azasypkin/kroneum/hw/pcb/Rev_0.6/demo/kroneum-pcb.png

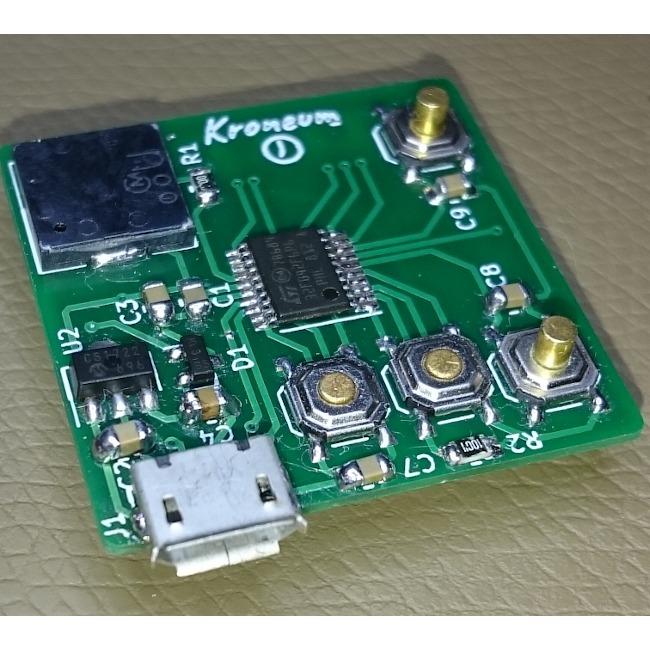
hw/pcb/Rev_0.6/demo/kroneum-pcb.png
