azasypkin/kroneum/sw/firmware/api/src/usb/commands.rs

mod adc;
mod alarm;
mod beeper;
mod flash;
mod keyboard;
mod radio;
mod system;

pub use self::adc::ADCCommand;
pub use self::alarm::AlarmCommand;
pub use self::beeper::BeeperCommand;
pub use self::flash::FlashCommand;
pub use self::keyboard::{KeyModifiers, KeyboardCommand, MediaKey};
pub use self::radio::RadioCommand;
pub use self::system::SystemCommand;
