azasypkin/kroneum/sw/cli/src/ui.rs

use crate::device::{Device, DeviceInfo};
use actix_files as fs;
use actix_web::{web, App, HttpResponse, HttpServer, Responder};
use core::convert::TryFrom;
use kroneum_api::{
    adc::ADCChannel,
    beeper::tone::Tone,
    flash::storage_slot::StorageSlot,
    time::Time,
    usb::commands::{KeyModifiers, MediaKey},
};
use serde_derive::{Deserialize, Serialize};

#[derive(Deserialize)]
struct ADCParams {
    channel: u8,
}

#[derive(Deserialize)]
#[serde(remote = "KeyModifiers")]
struct KeyModifiersDef {
    #[serde(rename(deserialize = "leftCtrl"))]
    left_ctrl: bool,
    #[serde(rename(deserialize = "leftShift"))]
    left_shift: bool,
    #[serde(rename(deserialize = "leftAlt"))]
    left_alt: bool,
    #[serde(rename(deserialize = "leftGUI"))]
    left_gui: bool,
    #[serde(rename(deserialize = "rightCtrl"))]
    right_ctrl: bool,
    #[serde(rename(deserialize = "rightShift"))]
    right_shift: bool,
    #[serde(rename(deserialize = "rightAlt"))]
    right_alt: bool,
    #[serde(rename(deserialize = "rightGUI"))]
    right_gui: bool,
}

#[derive(Deserialize)]
struct KeyParams {
    #[serde(rename(deserialize = "keyCode"))]
    key_code: u8,
    delay: u8,
    #[serde(with = "KeyModifiersDef")]
    modifiers: KeyModifiers,
}

#[derive(Deserialize)]
struct MediaKeyParams {
    #[serde(rename(deserialize = "keyCode"))]
    key_code: u8,
    delay: u8,
}

#[derive(Serialize)]
struct SystemInfoResponse {
    id: String,
    #[serde(rename(serialize = "flashSizeKb"))]
    flash_size_kb: u16,
}

#[derive(Serialize)]
struct InfoResponse {
    device: DeviceInfo,
    system: SystemInfoResponse,
}

#[derive(Deserialize)]
struct SetAlarmParams {
    alarm: String,
}

#[derive(Deserialize)]
struct WriteFlashParams {
    slot: u8,
    value: u8,
}

async fn adc(params: web::Path<ADCParams>) -> impl Responder {
    match ADCChannel::try_from(params.channel) {
        Ok(channel) => {
            HttpResponse::Ok().json(Device::create().unwrap().adc_read(channel).unwrap())
        }
        Err(message) => HttpResponse::BadRequest().body(message),
    }
}

async fn alarm_get() -> impl Responder {
    let device = Device::create().unwrap();
    let alarm = Time::from_seconds(device.get_alarm().unwrap().as_secs() as u32);
    HttpResponse::Ok().json(format!(
        "{:02}h {:02}m {:02}s",
        alarm.hours, alarm.minutes, alarm.seconds
    ))
}

async fn alarm_set(alarm: web::Json<SetAlarmParams>) -> impl Responder {
    match alarm
        .0
        .alarm
        .parse::<humantime::Duration>()
        .or_else(|err| Err(format!("Failed to parse alarm: {:?}", err)))
    {
        Ok(duration) => match Device::create().unwrap().set_alarm(duration.into()) {
            Ok(_) => HttpResponse::NoContent().finish(),
            Err(message) => HttpResponse::InternalServerError().body(message),
        },
        Err(message) => HttpResponse::BadRequest().body(message),
    }
}

async fn beep() -> impl Responder {
    let device = Device::create().unwrap();
    device.beeper_beep(1).unwrap();
    HttpResponse::NoContent()
}

async fn echo(info: web::Json<Vec<u8>>) -> impl Responder {
    HttpResponse::Ok().json(
        Device::create()
            .unwrap()
            .system_echo(info.as_ref())
            .unwrap(),
    )
}

async fn radio_transmit(info: web::Json<Vec<u8>>) -> impl Responder {
    match Device::create().unwrap().radio_transmit(info.as_ref()) {
        Ok(_) => HttpResponse::NoContent().finish(),
        Err(message) => HttpResponse::InternalServerError().body(message),
    }
}

async fn radio_receive() -> impl Responder {
    HttpResponse::Ok().json(Device::create().unwrap().radio_receive().unwrap())
}

async fn radio_status() -> impl Responder {
    HttpResponse::Ok().json(Device::create().unwrap().radio_status().unwrap())
}

async fn play(tones: web::Json<Vec<(u8, u8)>>) -> impl Responder {
    let device = Device::create().unwrap();
    device
        .beeper_melody(
            tones
                .iter()
                .map(|(note, duration)| Tone::new(*note, *duration))
                .collect::<Vec<Tone>>()
                .as_ref(),
        )
        .unwrap();
    HttpResponse::NoContent()
}

async fn flash_read() -> impl Responder {
    let device = Device::create().unwrap();
    HttpResponse::Ok().json(vec![
        device.read_flash(StorageSlot::Configuration).unwrap(),
        device.read_flash(StorageSlot::Custom(1)).unwrap(),
        device.read_flash(StorageSlot::Custom(2)).unwrap(),
        device.read_flash(StorageSlot::Custom(3)).unwrap(),
        device.read_flash(StorageSlot::Custom(4)).unwrap(),
    ])
}

async fn flash_write(flash: web::Json<WriteFlashParams>) -> impl Responder {
    match StorageSlot::try_from(flash.slot) {
        Ok(slot) => match Device::create().unwrap().write_flash(slot, flash.value) {
            Ok(_) => HttpResponse::NoContent().finish(),
            Err(message) => HttpResponse::InternalServerError().body(message),
        },
        Err(_) => {
            HttpResponse::BadRequest().body(format!("Failed to parse slot: {:?}", flash.slot))
        }
    }
}

async fn flash_erase() -> impl Responder {
    match Device::create().unwrap().erase_flash() {
        Ok(_) => HttpResponse::NoContent().finish(),
        Err(message) => HttpResponse::InternalServerError().body(message),
    }
}

async fn get_info() -> impl Responder {
    let device = Device::create().unwrap();
    match device.system_get_info() {
        Ok(system) => {
            let mut system_id = [0u8; 16];
            system.id.iter().enumerate().for_each(|(index, byte)| {
                system_id[index + 4] = *byte;
            });
            HttpResponse::Ok().json(InfoResponse {
                device: device.get_info(),
                system: SystemInfoResponse {
                    id: format!("{:#x?}", u128::from_be_bytes(system_id)),
                    flash_size_kb: system.flash_size_kb,
                },
            })
        }
        Err(message) => HttpResponse::InternalServerError().body(message),
    }
}

async fn send_key(params: web::Json<KeyParams>) -> impl Responder {
    let device = Device::create().unwrap();
    device
        .keyboard_key(params.modifiers, params.key_code, params.delay)
        .unwrap();
    HttpResponse::NoContent()
}

async fn send_media_key(params: web::Json<MediaKeyParams>) -> impl Responder {
    match MediaKey::try_from(params.key_code) {
        Ok(media_key) => {
            Device::create()
                .unwrap()
                .keyboard_media_key(media_key, params.delay)
                .unwrap();
            HttpResponse::NoContent().finish()
        }
        Err(_) => {
            HttpResponse::BadRequest().body(format!("Not supported media key: {}", params.key_code))
        }
    }
}

#[actix_rt::main]
pub async fn run_server(port: u16) -> Result<(), String> {
    let ui_url = format!("127.0.0.1:{}", port);
    let http_server = HttpServer::new(|| {
        App::new()
            .route("/api/alarm", web::get().to(alarm_get))
            .route("/api/alarm/set", web::post().to(alarm_set))
            .route("/api/beep", web::get().to(beep))
            .route("/api/play", web::post().to(play))
            .route("/api/flash", web::get().to(flash_read))
            .route("/api/flash/write", web::post().to(flash_write))
            .route("/api/flash/erase", web::post().to(flash_erase))
            .route("/api/info", web::get().to(get_info))
            .route("/api/echo", web::post().to(echo))
            .route("/api/radio/receive", web::get().to(radio_receive))
            .route("/api/radio/transmit", web::post().to(radio_transmit))
            .route("/api/radio/status", web::get().to(radio_status))
            .route("/api/adc/{channel}", web::get().to(adc))
            .route("/api/key", web::post().to(send_key))
            .route("/api/media_key", web::post().to(send_media_key))
            .service(fs::Files::new("/", "./src/ui/static/dist").index_file("index.html"))
    })
    .bind(&ui_url)
    .or_else(|err| Err(format!("Failed to bind to {}: {:?}", &ui_url, err)))?;

    println!("Running Kroneum Web UI on http://{}", ui_url);

    http_server
        .run()
        .await
        .or_else(|err| Err(format!("Failed to run Web Server {:?}", err)))
}
